ctranstrum/chuck/images/chuck-blue.jpg

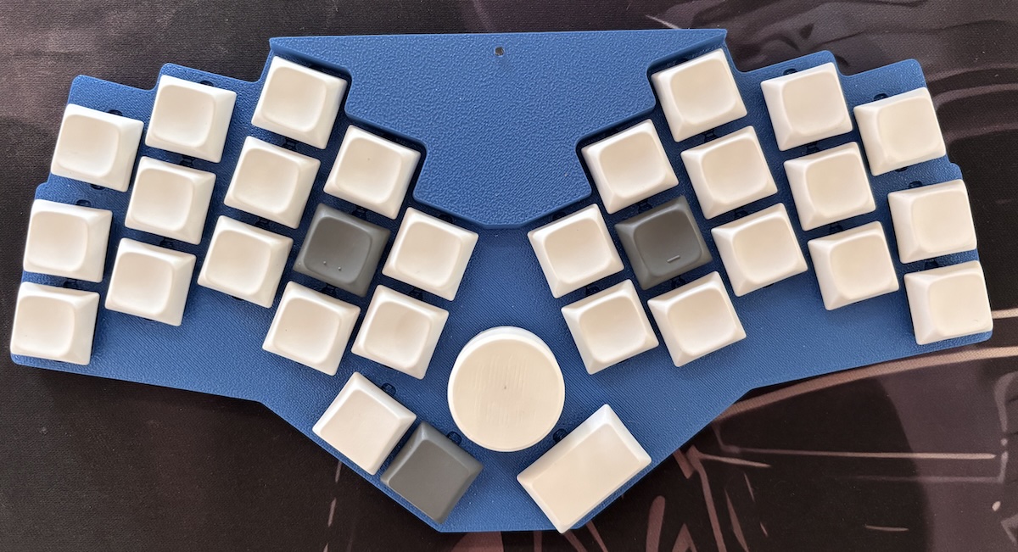
images/chuck-blue.jpg
