ctranstrum/chuck/images/fingering.jpg

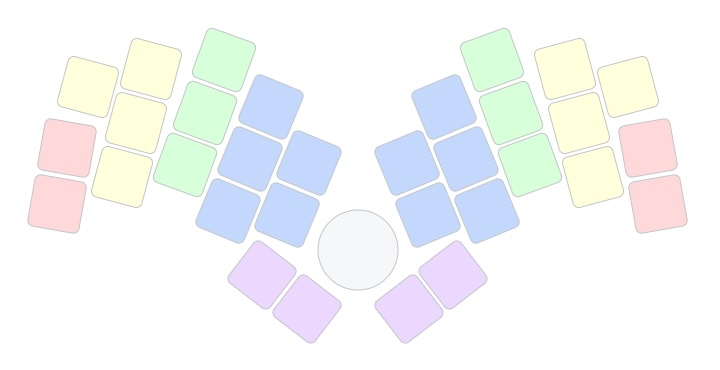
images/fingering.jpg
