ctranstrum/chuck/images/rectangle-back.jpg

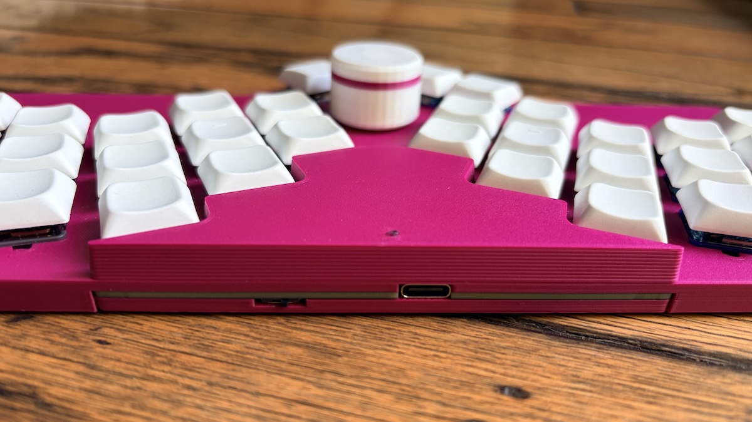
images/rectangle-back.jpg
